msjun23/Capstone-2022/images/meeting/0411_1.jpg

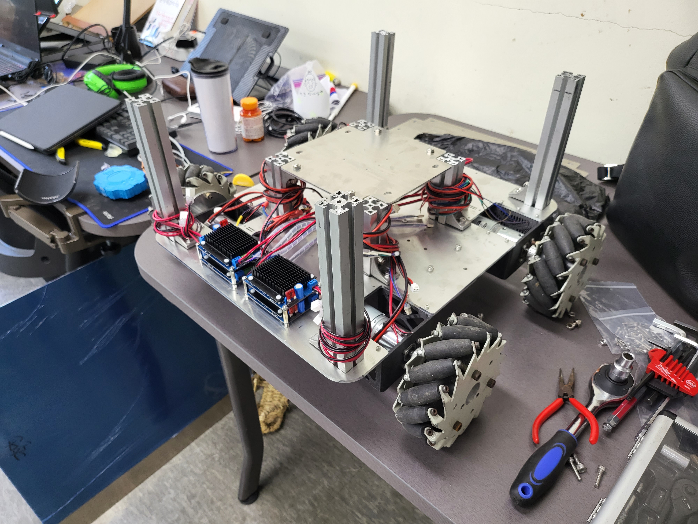
images/meeting/0411_1.jpg
